davift/BLR-300/PCB_Back_Big.jpg

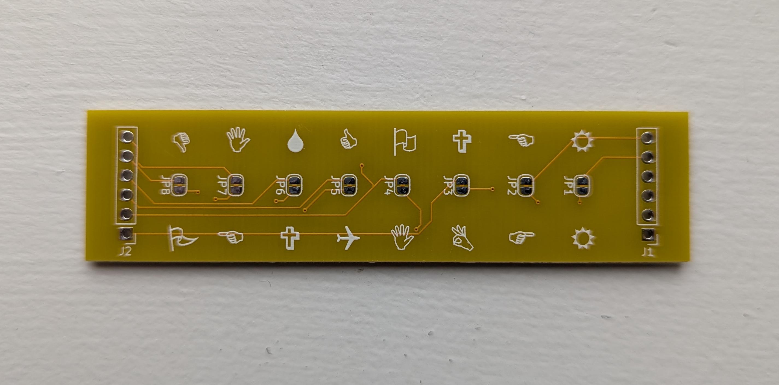
PCB_Back_Big.jpg
