davift/BLR-300/PCB_Backlight_Big.jpg

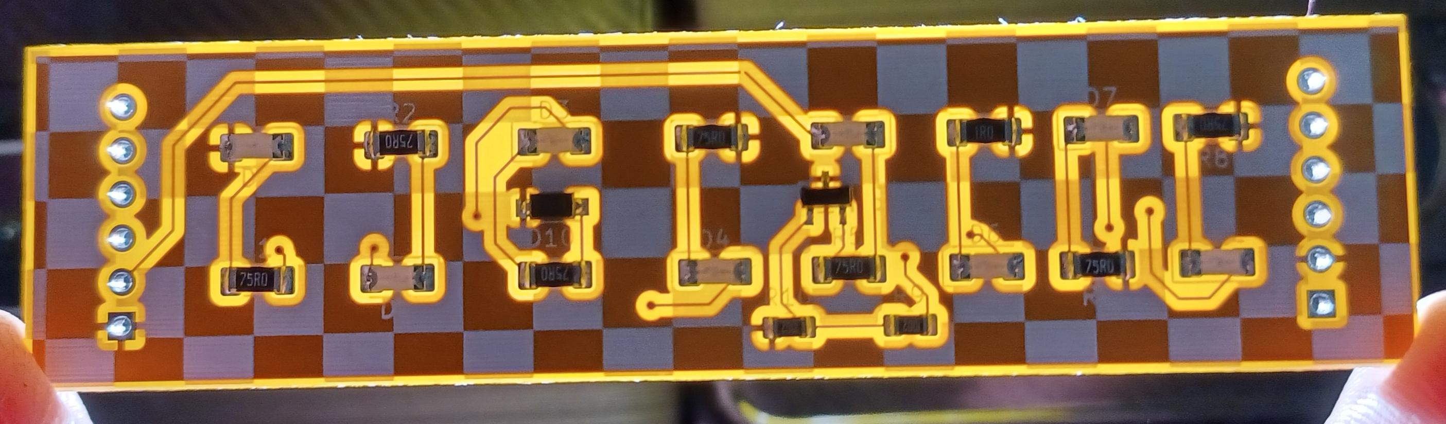
PCB_Backlight_Big.jpg
