davift/BLR-300/PCB_Front_Big.jpg

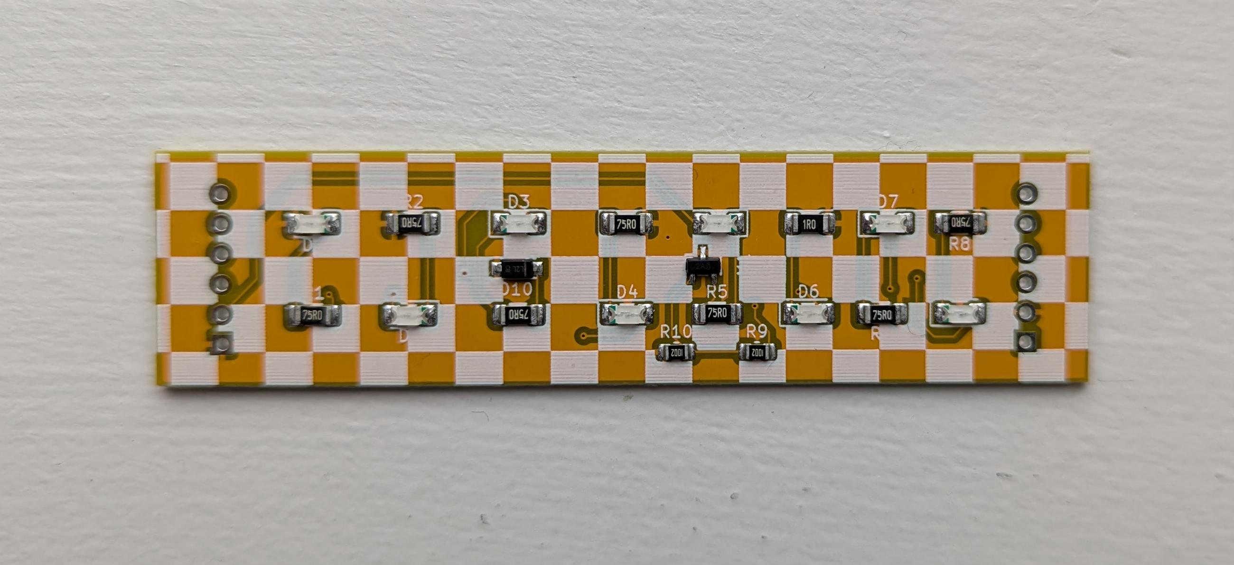
PCB_Front_Big.jpg
