davift/BLR-300/BLR-300.kicad_pcb

## KiCad design reverse_ecobeemux_175-00011-revD.kicad_sch

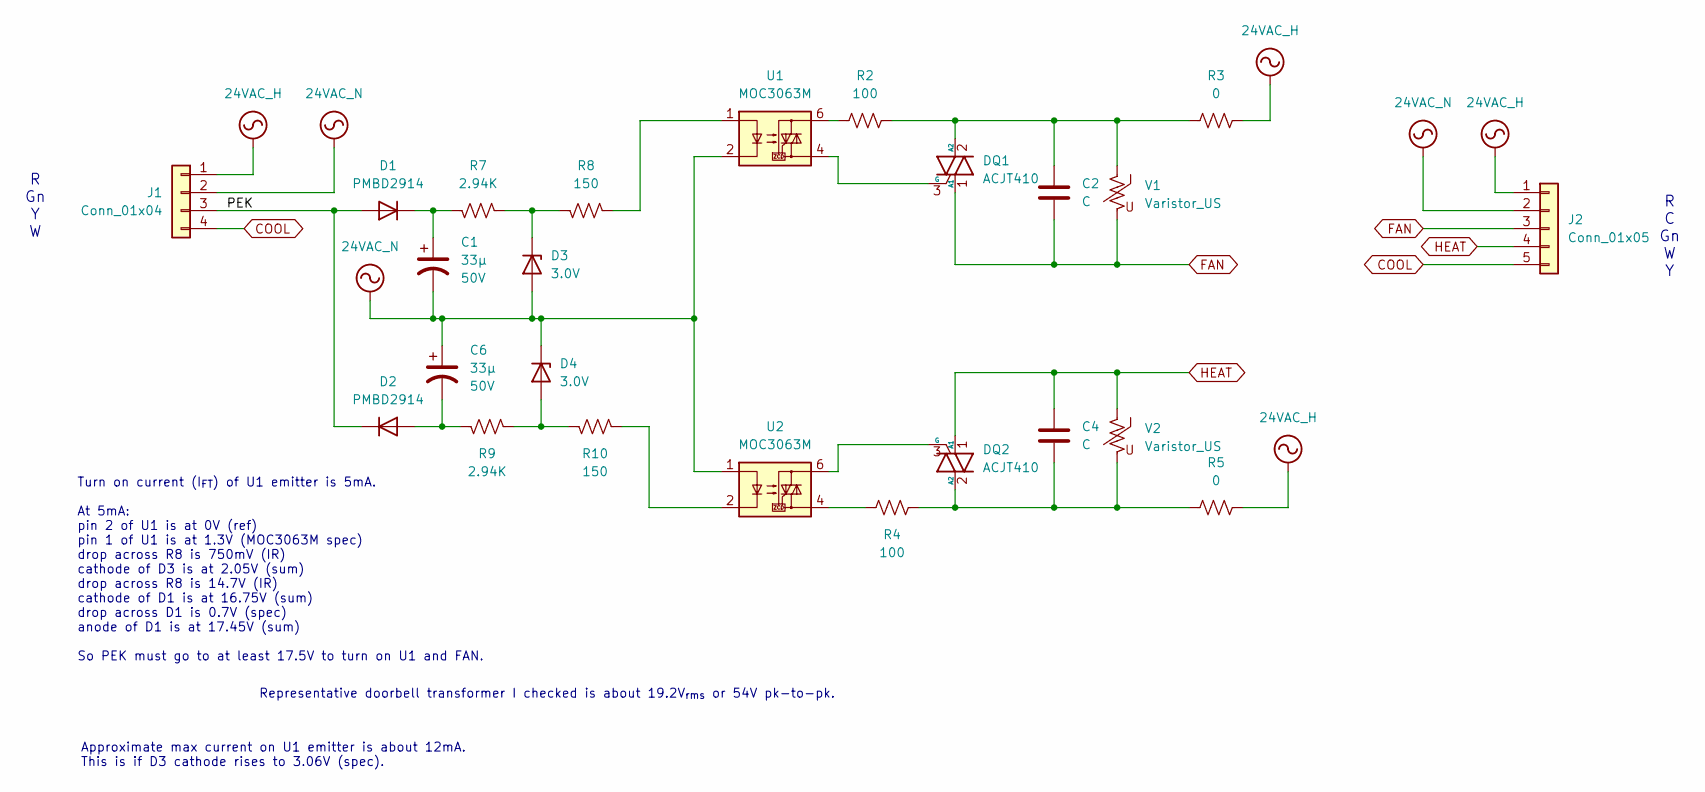
[picture p23: schematic reverse_ecobeemux_175-00011-revD.kicad_sch]

Parts:
C1, C6: 33µ; Voltage 50V
C2, C4: C
D1, D2: PMBD2914
D3, D4: 3.0V
DQ1, DQ2: ACJT410
J1: Conn_01x04
J2: Conn_01x05
R2, R4: 100
R3, R5: 0
R7, R9: 2.94K
R8, R10: 150
U1, U2: MOC3063M
V1, V2: Varistor_US

Connections:
24VAC_H: J1.1, J2.1, R3.2, R5.2
24VAC_N: C1.2, C6.1, D3.2 (A), D4.1 (K), J1.2, J2.2, U1.2, U2.1
COOL: J1.4, J2.5
FAN: C2.1, DQ1.1 (A1), J2.3, V1.2
HEAT: C4.2, DQ2.1 (A1), J2.4, V2.1
unnamed: C1.1, D1.1 (K), R7.2
unnamed: C2.2, DQ1.2 (A2), R2.2, R3.1, V1.1
unnamed: C4.1, DQ2.2 (A2), R4.2, R5.1, V2.2
unnamed: C6.2, D2.2 (A), R9.2
unnamed: D3.1 (K), R7.1, R8.2
unnamed: D4.2 (A), R9.1, R10.2
unnamed: DQ1.3 (G), U1.4
unnamed: DQ2.3 (G), U2.6
unnamed: R2.1, U1.6
unnamed: R4.1, U2.4
unnamed: R8.1, U1.1
unnamed: R10.1, U2.2
PEK: D1.2 (A), D2.1 (K), J1.3

Notes on the sheet:
R Gn Y W
R C Gn W Y
Turn on current (I_{FT}) of U1 emitter is 5mA. At 5mA: pin 2 of U1 is at 0V (ref) pin 1 of U1 is at 1.3V (MOC3063M spec) drop across R8 is 750mV (IR) cathode of D3 is at 2.05V (sum) drop across R8 is 14.7V (IR) cathode of D1 is at 16.75V (sum) drop across D1 is 0.7V (spec) anode of D1 is at 17.45V 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
Representative doorbell transformer I checked is about 19.2V_{rms} or 54V pk-to-pk.
Approximate max current on U1 emitter is about 12mA. This is if D3 cathode rises to 3.06V (spec).
